TinyCircuits/TinyCircuits-Wireling-0.42-Screen-OLED-AST1042/cad/Wireling_042OLED_AST1042_REV1-DETAILED_DRAWING_COMPACT-PNG.png

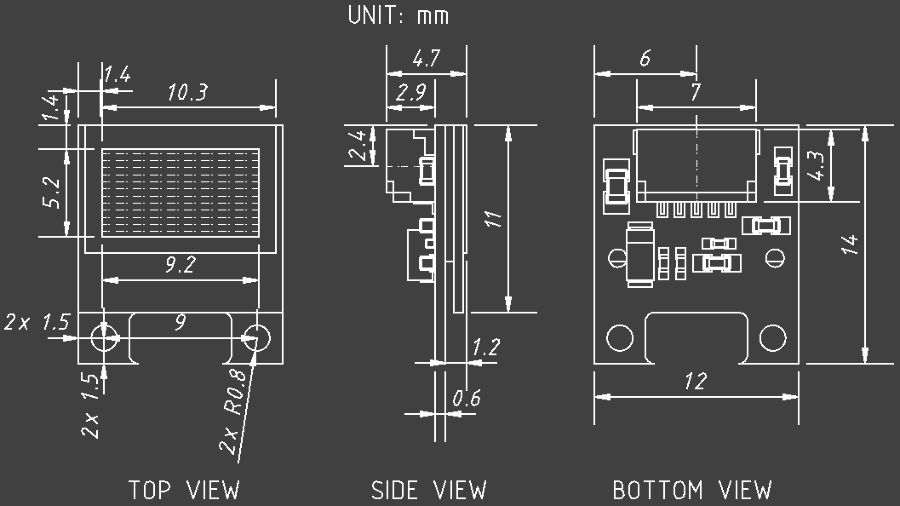
cad/Wireling_042OLED_AST1042_REV1-DETAILED_DRAWING_COMPACT-PNG.png
