TinyCircuits/TinyCircuits-Wireling-0.42-Screen-OLED-AST1042/images/AST1042-Product-Photo-01.2.png

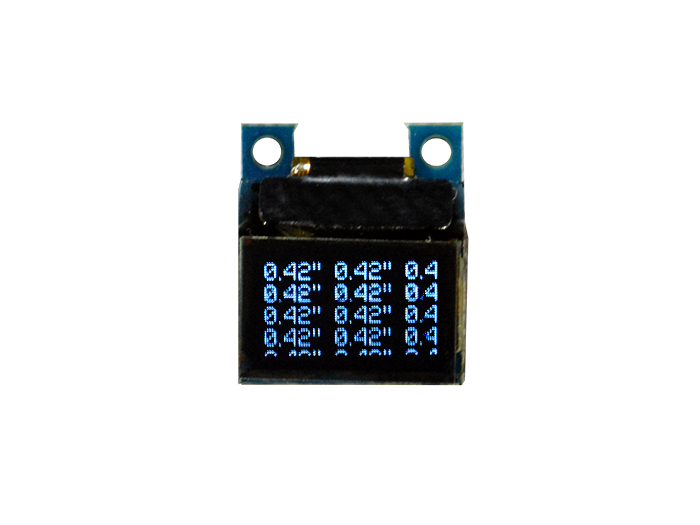
images/AST1042-Product-Photo-01.2.png
