TinyCircuits/TinyCircuits-Wireling-0.42-Screen-OLED-AST1042/images/AST1042-Tutorial-Animation-01.gif

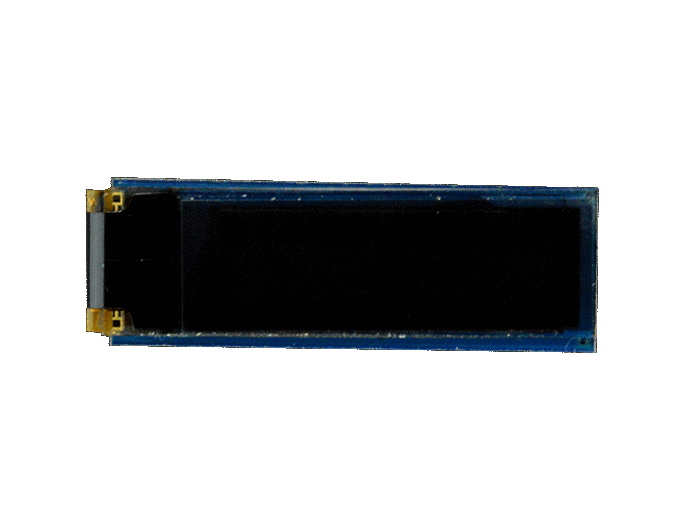
images/AST1042-Tutorial-Animation-01.gif
