TinyCircuits/TinyCircuits-Wireling-0.42-Screen-OLED-AST1042/images/AST1042-Tutorial-Image-01.png

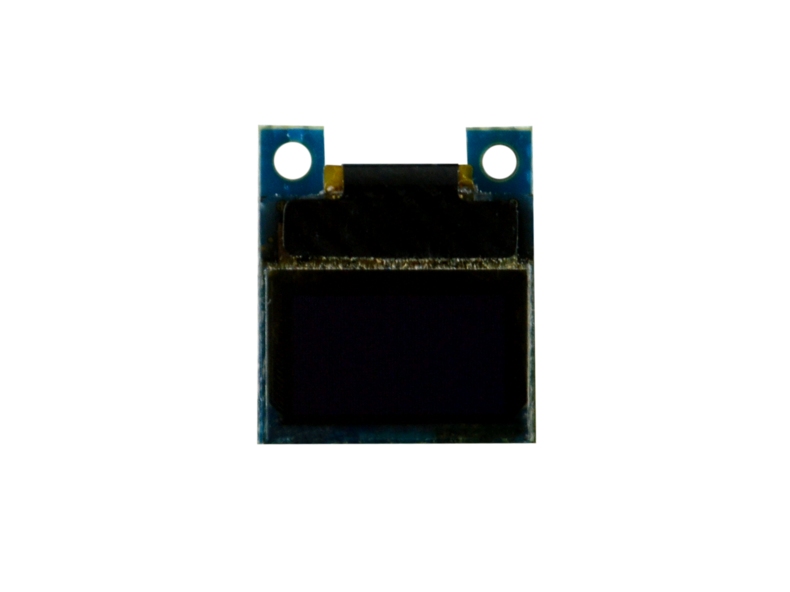
images/AST1042-Tutorial-Image-01.png
